3dprintingworld/Linear-Actuator/DL1/STL/LA-007.stl

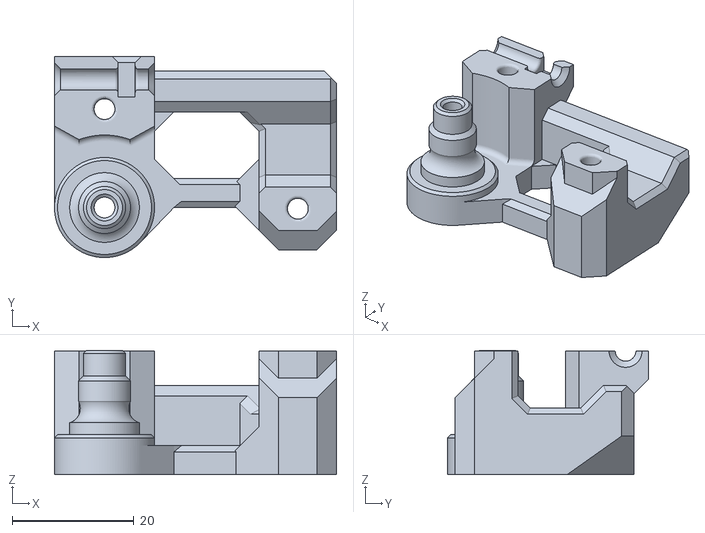
[picture p24: CAD file, 2020-11-26]
DL1/STL/LA-007.stl
46.3 x 33.0 x 20.4
