3dprintingworld/Linear-Actuator/DL2/STL's/LA-DL2-012.stl

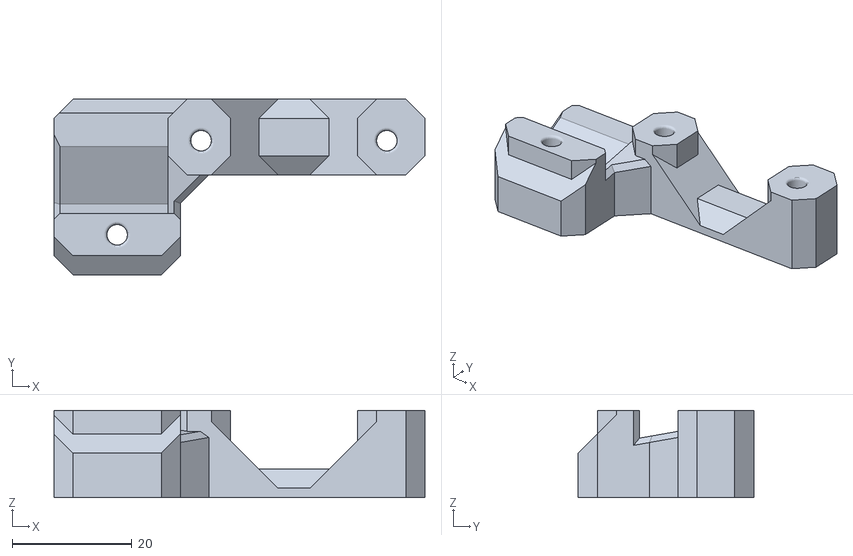
[picture p25: CAD file, 2021-02-14]
DL2/STL's/LA-DL2-012.stl
61.9 x 29.3 x 14.6
