3dprintingworld/Linear-Actuator/DL1/STL/LA-002.stl

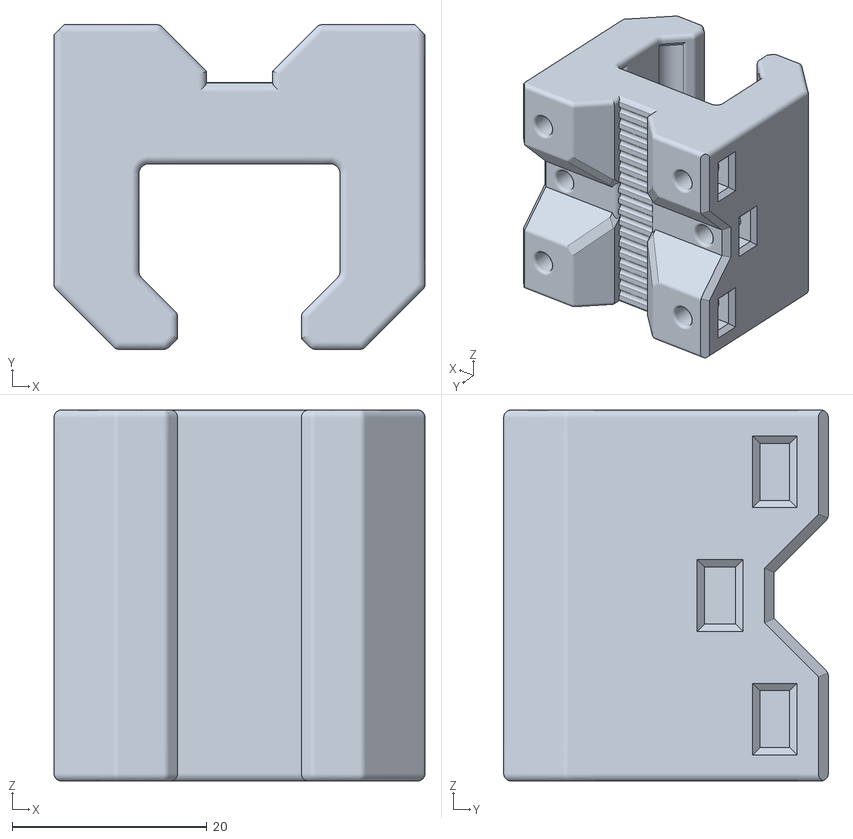
[picture p26: CAD file, 2020-11-26]
DL1/STL/LA-002.stl
38.1 x 33.3 x 38.1
