3dprintingworld/Linear-Actuator/DL2/STL's/LA-DL2-006.stl

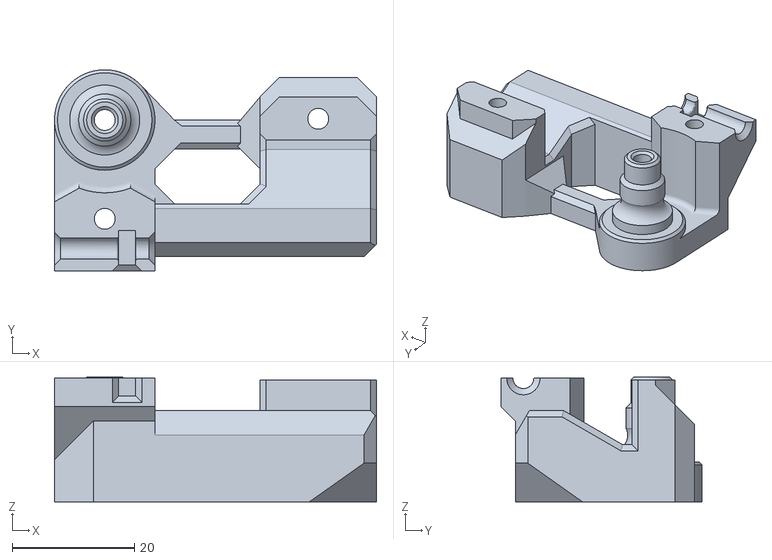
[picture p27: CAD file, 2021-02-14]
DL2/STL's/LA-DL2-006.stl
52.7 x 32.9 x 20.4
