3dprintingworld/Linear-Actuator/DL1/STL/LA-015.stl

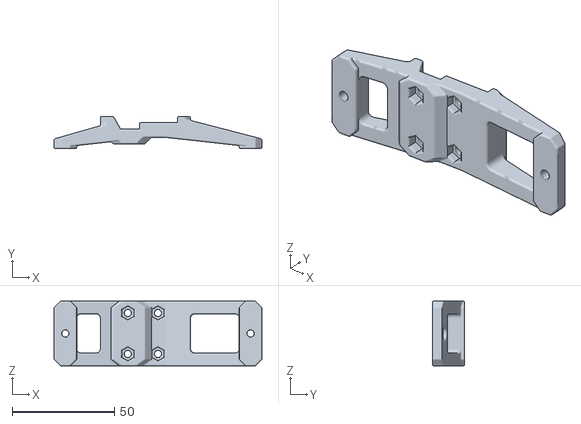
[picture p28: CAD file, 2020-11-26]
DL1/STL/LA-015.stl
101.6 x 15.9 x 31.7
