3dprintingworld/Linear-Actuator/DL2/STL's/LA-DL2-007.stl

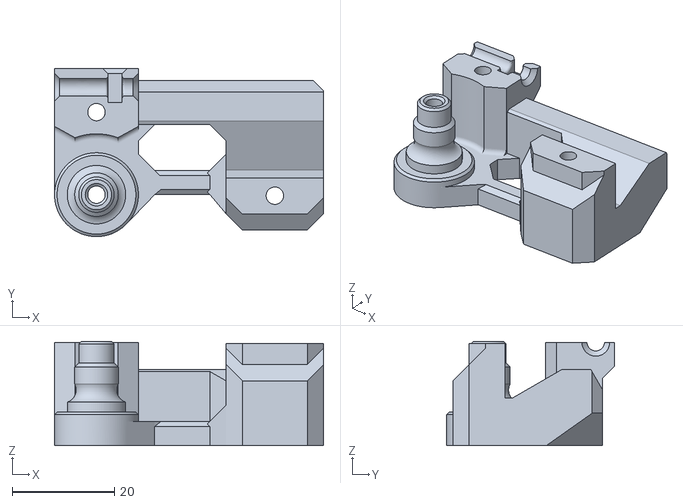
[picture p29: CAD file, 2021-02-14]
DL2/STL's/LA-DL2-007.stl
52.7 x 32.9 x 20.4
