3dprintingworld/Linear-Actuator/DL2/STL's/LA-DL2-002.stl

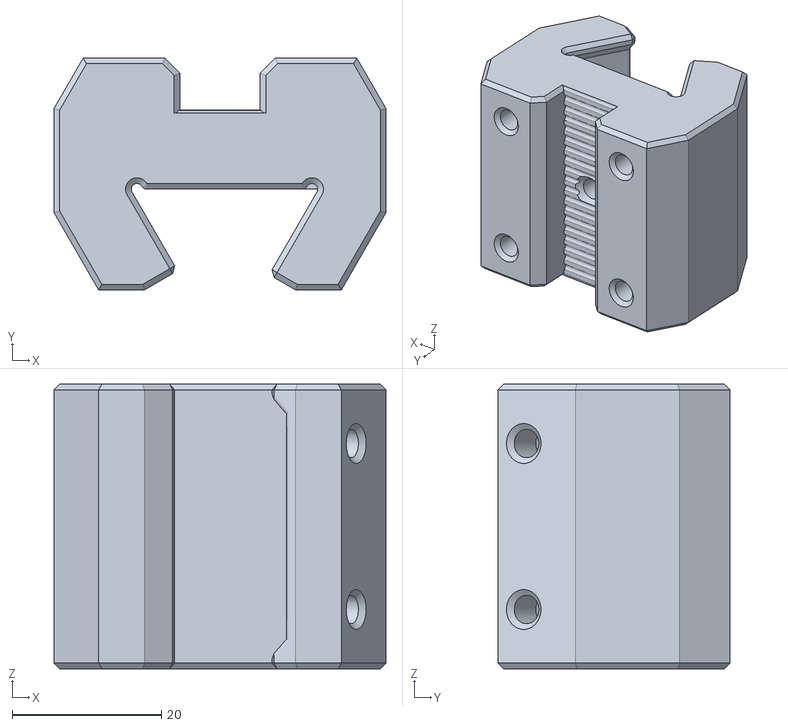
[picture p30: CAD file, 2021-02-14]
DL2/STL's/LA-DL2-002.stl
44.5 x 31.1 x 38.1
