3dprintingworld/Linear-Actuator/DL1/STL/LA-003.stl

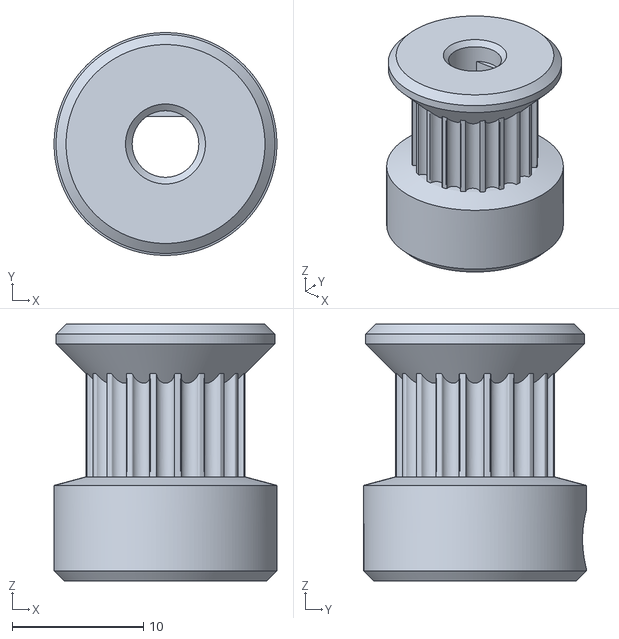
[picture p31: CAD file, 2020-11-26]
DL1/STL/LA-003.stl
17.0 x 17.0 x 19.6
