3dprintingworld/Linear-Actuator/DL2/STL's/LA-DL2-020.stl

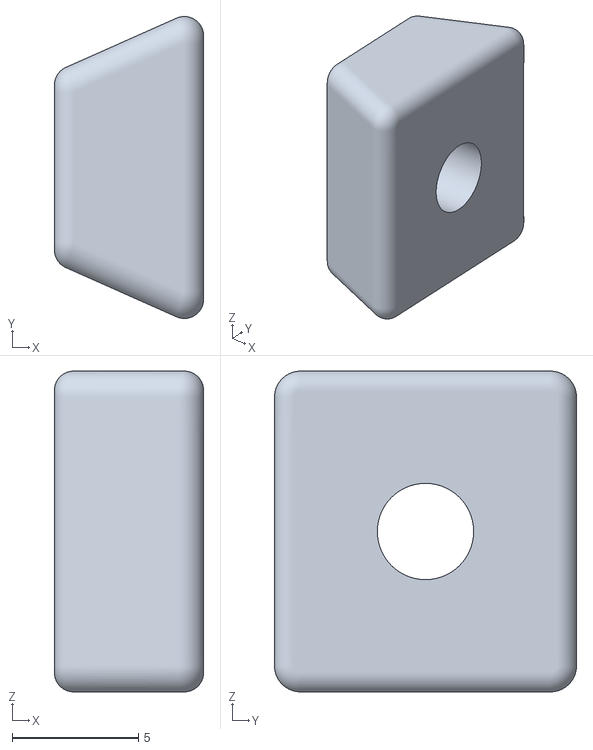
[picture p32: CAD file, 2021-02-14]
DL2/STL's/LA-DL2-020.stl
5.91 x 12.0 x 12.7
