3dprintingworld/Linear-Actuator/DL2/STL's/LA-DL2-016.stl

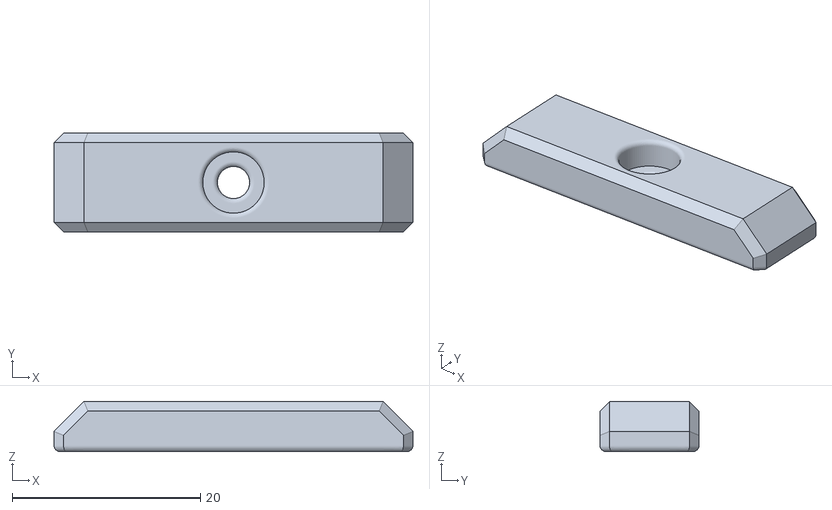
[picture p33: CAD file, 2021-02-14]
DL2/STL's/LA-DL2-016.stl
38.1 x 10.5 x 5.31
